slowlane112/Esp32-Game-and-Watch/assets/menu/handheld_multi_screen_2_button/top_pinball.png

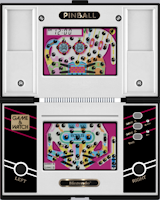
assets/menu/handheld_multi_screen_2_button/top_pinball.png
