slowlane112/Esp32-Game-and-Watch/assets/menu/handheld_multi_screen_dpad/bottom_donkey_kong_ii.png

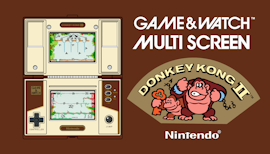
assets/menu/handheld_multi_screen_dpad/bottom_donkey_kong_ii.png
