slowlane112/Esp32-Game-and-Watch/assets/menu/handheld_multi_screen_dpad/bottom_zelda.png

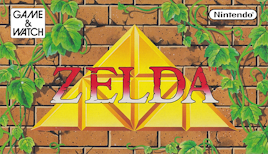
assets/menu/handheld_multi_screen_dpad/bottom_zelda.png
