slowlane112/Esp32-Game-and-Watch/assets/menu/handheld_multi_screen_dpad/top_donkey_kong.png

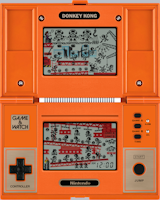
assets/menu/handheld_multi_screen_dpad/top_donkey_kong.png
