slowlane112/Esp32-Game-and-Watch/assets/menu/handheld_single_screen_2_button/mario_the_juggler.png

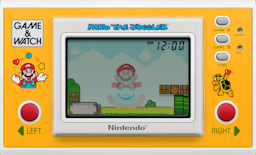
assets/menu/handheld_single_screen_2_button/mario_the_juggler.png
