slowlane112/Esp32-Game-and-Watch/assets/menu/handheld_single_screen_2_button/tropical_fish.png

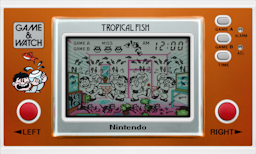
assets/menu/handheld_single_screen_2_button/tropical_fish.png
