slowlane112/Esp32-Game-and-Watch/assets/menu/handheld_single_screen_4_button/marios_cement_factory.png

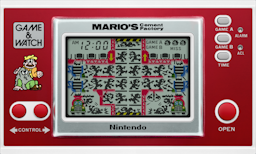
assets/menu/handheld_single_screen_4_button/marios_cement_factory.png
