slowlane112/Esp32-Game-and-Watch/assets/3d_files/gandw_single_screen_4button_handheld/alarm_acl_button_spacer.stl

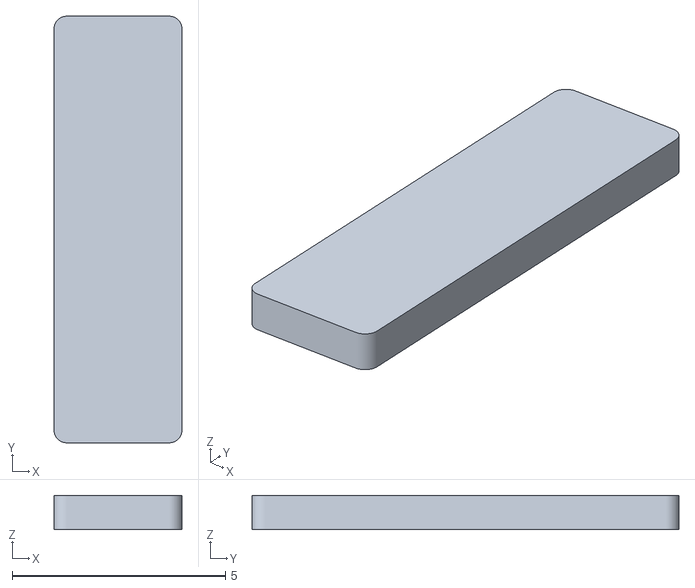
[picture p112: CAD file, 2025-06-24]
assets/3d_files/gandw_single_screen_4button_handheld/alarm_acl_button_spacer.stl
3.00 x 10.0 x 0.8
