slowlane112/Esp32-Game-and-Watch/assets/3d_files/gandw_single_screen_4button_handheld/small_button.stl

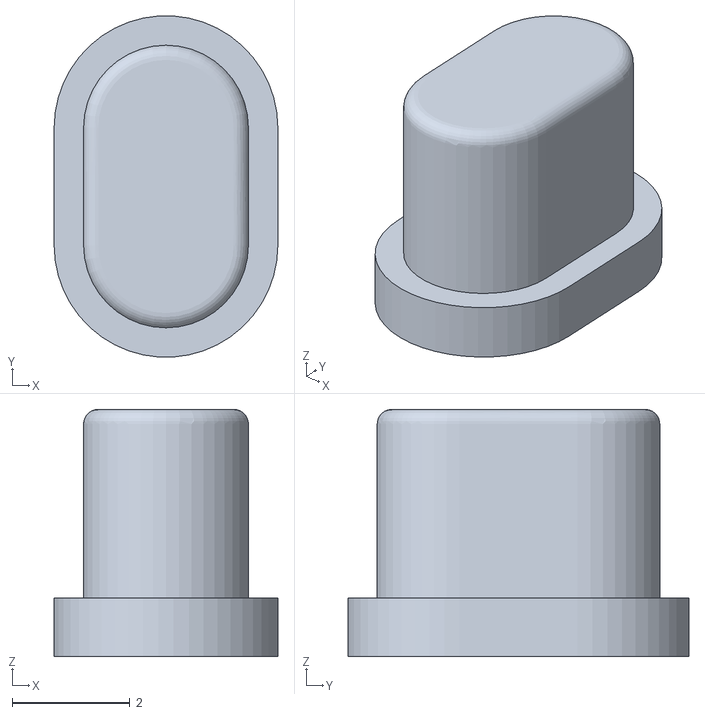
[picture p113: CAD file, 2025-06-24]
assets/3d_files/gandw_single_screen_4button_handheld/small_button.stl
3.80 x 5.79 x 4.20
