slowlane112/Esp32-Game-and-Watch/assets/3d_files/gandw_multi_screen_dpad_handheld/top_case_back.stl

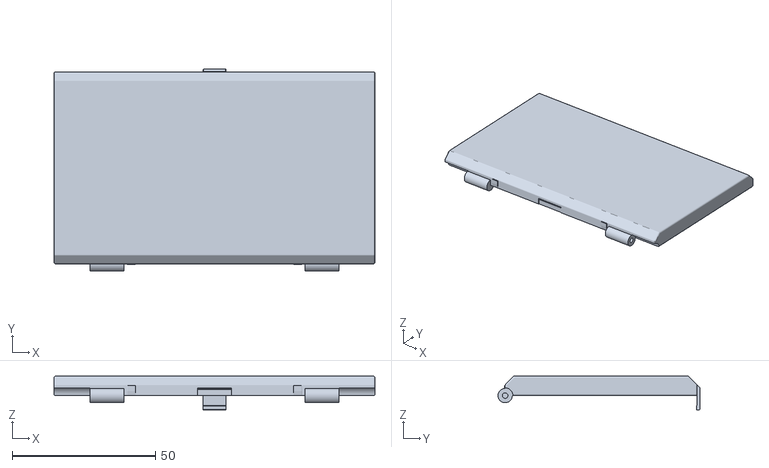
[picture p114: CAD file, 2025-07-19]
assets/3d_files/gandw_multi_screen_dpad_handheld/top_case_back.stl
112.0 x 70.5 x 11.8
