slowlane112/Esp32-Game-and-Watch/assets/3d_files/gandw_single_screen_4button_handheld/esp32_mount.stl

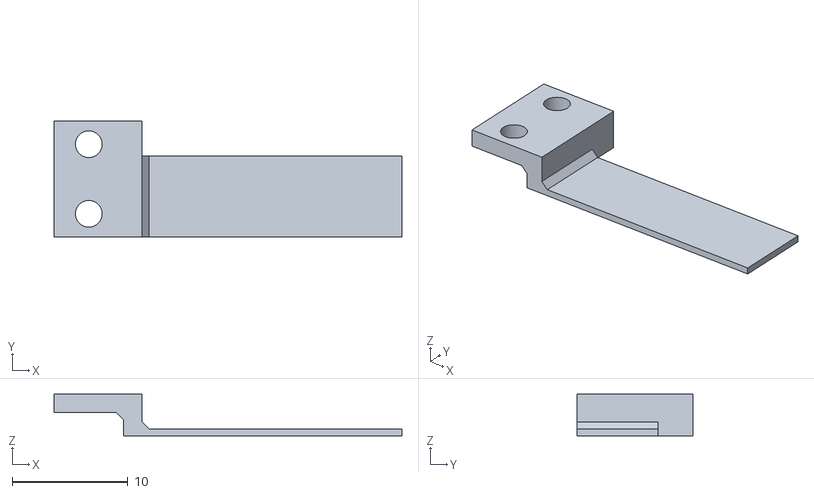
[picture p115: CAD file, 2025-06-24]
assets/3d_files/gandw_single_screen_4button_handheld/esp32_mount.stl
30.0 x 10.0 x 3.60
