slowlane112/Esp32-Game-and-Watch/assets/3d_files/gandw_multi_screen_dpad_handheld/bottom_case_front_part_hinge.stl

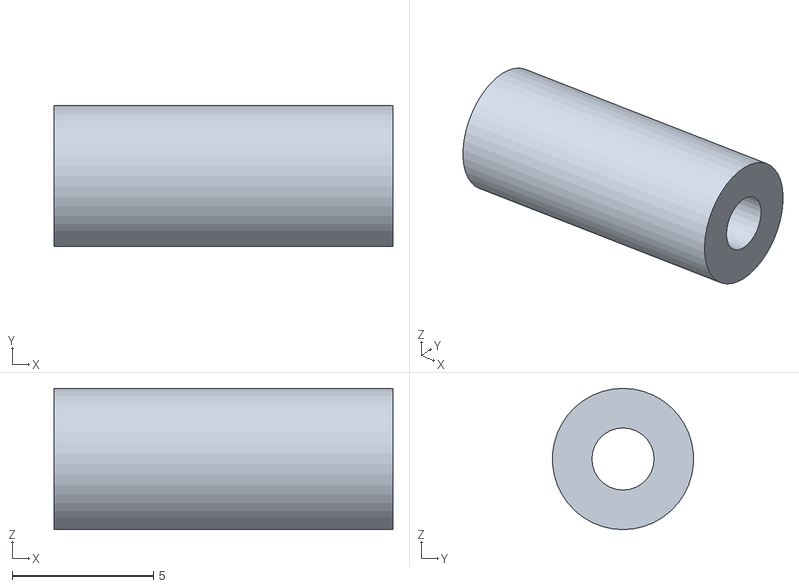
[picture p116: CAD file, 2025-07-19]
assets/3d_files/gandw_multi_screen_dpad_handheld/bottom_case_front_part_hinge.stl
12.0 x 4.99 x 5.00
