slowlane112/Esp32-Game-and-Watch/gandw_handheld/main/pixel_font.c

unsigned char pixel_font[] = {
	
	// char 000
	0b11111111,
	0b11000011,
	0b10011001,
	0b10010001,
	0b10010001,
	0b10011111,
	0b11000011,
	0b11111111,

	// char 001
	0b11111111,
	0b11000011,
	0b10011001,
	0b10011001,
	0b10000001,
	0b10011001,
	0b10011001,
	0b11111111,

	// char 002
	0b11111111,
	0b10000011,
	0b10011001,
	0b10000011,
	0b10011001,
	0b10011001,
	0b10000011,
	0b11111111,

	// char 003
	0b11111111,
	0b11000001,
	0b10011111,
	0b10011111,
	0b10011111,
	0b10011111,
	0b11000001,
	0b11111111,

	// char 004
	0b11111111,
	0b10000011,
	0b10011001,
	0b10011001,
	0b10011001,
	0b10011001,
	0b10000011,
	0b11111111,

	// char 005
	0b11111111,
	0b10000001,
	0b10011111,
	0b10000011,
	0b10011111,
	0b10011111,
	0b10000001,
	0b11111111,

	// char 006
	0b11111111,
	0b10000001,
	0b10011111,
	0b10000011,
	0b10011111,
	0b10011111,
	0b10011111,
	0b11111111,

	// char 007
	0b11111111,
	0b11000001,
	0b10011111,
	0b10010001,
	0b10011001,
	0b10011001,
	0b11000001,
	0b11111111,

	// char 008
	0b11111111,
	0b10011001,
	0b10011001,
	0b10000001,
	0b10011001,
	0b10011001,
	0b10011001,
	0b11111111,

	// char 009
	0b11111111,
	0b11000011,
	0b11100111,
	0b11100111,
	0b11100111,
	0b11100111,
	0b11000011,
	0b11111111,

	// char 010
	0b11111111,
	0b11100011,
	0b11110011,
	0b11110011,
	0b11110011,
	0b10010011,
	0b11000111,
	0b11111111,

	// char 011
	0b11111111,
	0b10011001,
	0b10010011,
	0b10000111,
	0b10000111,
	0b10010011,
	0b10011001,
	0b11111111,

	// char 012
	0b11111111,
	0b10011111,
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
	0b00000000,
	0b00011000,
	0b00000000,
	0b00000000,

	// char 248
	0b00000000,
	0b00000110,
	0b00111100,
	0b01101110,
	0b01110110,
	0b01110110,
	0b00111100,
	0b01100000,

	// char 249
	0b00110000,
	0b00011000,
	0b01100110,
	0b01100110,
	0b01100110,
	0b01100110,
	0b00111110,
	0b00000000,

	// char 250
	0b00001100,
	0b00011000,
	0b01100110,
	0b01100110,
	0b01100110,
	0b01100110,
	0b00111110,
	0b00000000,

	// char 251
	0b00111100,
	0b01000010,
	0b00000000,
	0b01100110,
	0b01100110,
	0b01100110,
	0b00111110,
	0b00000000,

	// char 252
	0b01100110,
	0b00000000,
	0b01100110,
	0b01100110,
	0b01100110,
	0b01100110,
	0b00111110,
	0b00000000,

	// char 253
	0b00001100,
	0b00011000,
	0b01100110,
	0b01100110,
	0b01100110,
	0b00111110,
	0b00000110,
	0b00111100,

	// char 254
	0b11110000,
	0b01100000,
	0b01111100,
	0b01100110,
	0b01111100,
	0b01100000,
	0b11110000,
	0b00000000,

	// char 255
	0b01100110,
	0b00000000,
	0b01100110,
	0b01100110,
	0b01100110,
	0b00111110,
	0b00000110,
	0b00111100

};

unsigned char pixel_font_get_data(int pos) {
	return pixel_font[pos];
}
