slowlane112/Esp32-Game-and-Watch/gandw_cardputer/main/volume.h

#ifndef VOLUME_H
#define VOLUME_H

#include "driver/i2s_std.h"

extern uint16_t volume ;
extern uint16_t volume_display_count;
void volume_read(void);
void volume_set(bool is_up);
void volume_display(unsigned short *framebuffer);
void volume_menu_tone(i2s_chan_handle_t i2s_handle);

#endif
